jacob23430434/Raspibery-pi-vision-car/schematics/MPU6050/MPU6050.kicad_pcb

## KiCad design electronics/ESP32/ESP32.kicad_sch

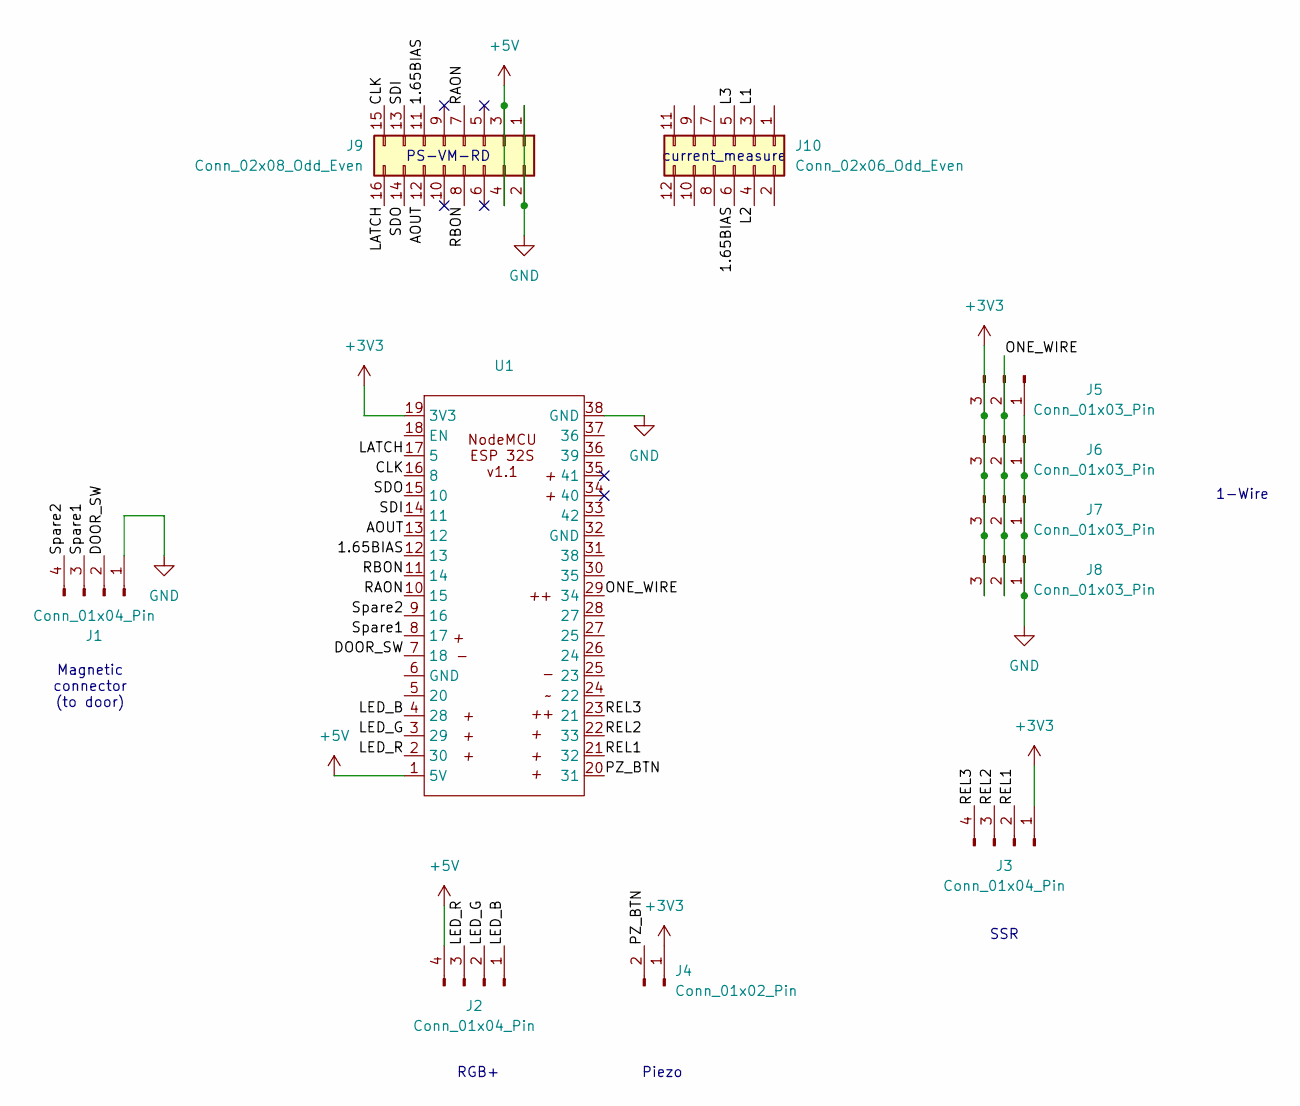
[picture p7: schematic ESP32.kicad_sch]

Parts:
J1, J2, J3: Conn_01x04_Pin
J4: Conn_01x02_Pin
J5, J6, J7, J8: Conn_01x03_Pin
J9: Conn_02x08_Odd_Even
J10: Conn_02x06_Odd_Even
U1: (no value)

Connections:
1.65BIAS: J9.11, J10.6, U1.12 (13)
+3V3: J3.1, J4.1, J5.3, J6.3, J7.3, J8.3, U1.19 (3V3)
+5V: J2.4, J9.3, J9.4, U1.1 (5V)
AOUT: J9.12, U1.13 (12)
CLK: J9.15, U1.16 (8)
DOOR_SW: J1.2, U1.7 (18)
GND: J1.1, J5.1, J6.1, J7.1, J8.1, J9.1, J9.2, U1.38 (GND)
L1: J10.3
L2: J10.4
L3: J10.5
LATCH: J9.16, U1.17 (5)
LED_B: J2.1, U1.4 (28)
LED_G: J2.2, U1.3 (29)
LED_R: J2.3, U1.2 (30)
ONE_WIRE: J5.2, J6.2, J7.2, J8.2, U1.29 (34)
PZ_BTN: J4.2, U1.20 (31)
RAON: J9.7, U1.10 (15)
RBON: J9.8, U1.11 (14)
REL1: J3.2, U1.21 (32)
REL2: J3.3, U1.22 (33)
REL3: J3.4, U1.23 (21)
SDI: J9.13, U1.14 (11)
SDO: J9.14, U1.15 (10)
Spare1: J1.3, U1.8 (17)
Spare2: J1.4, U1.9 (16)

Notes on the sheet:
1-Wire
current_measure
PS-VM-RD
SSR
Magnetic connector (to door)
RGB+
Piezo
